ernesto-g/arduinosynth2/Hardware/PCB/Sketch_etch_silk_bottom.pdf

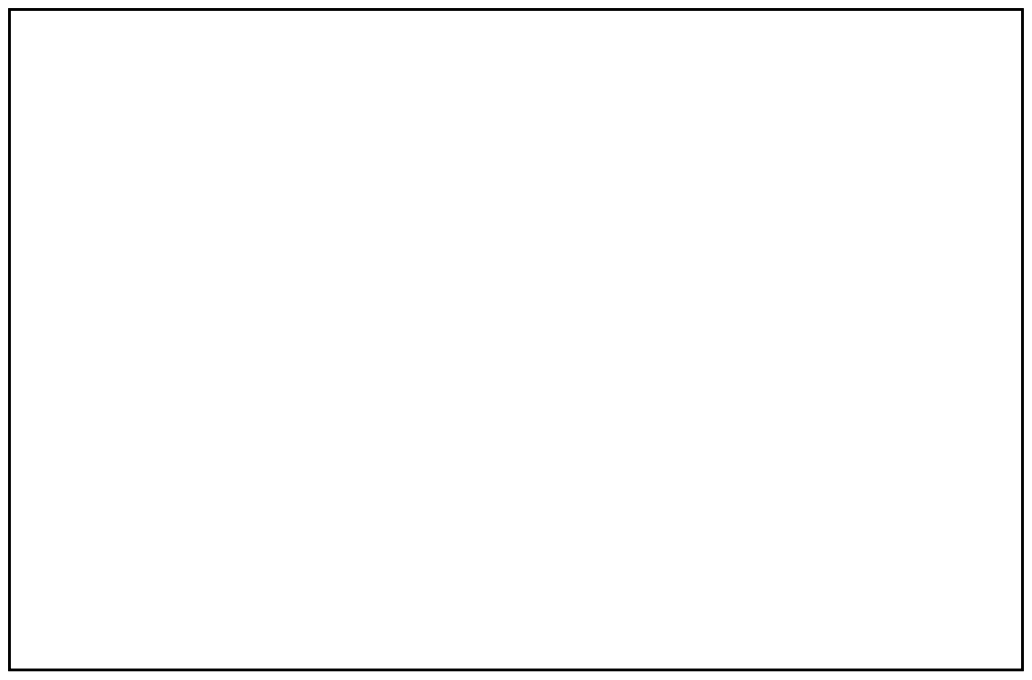
[picture p11: page 1]
