ernesto-g/arduinosynth2/Hardware/PCB/Sketch_etch_silk_top.pdf

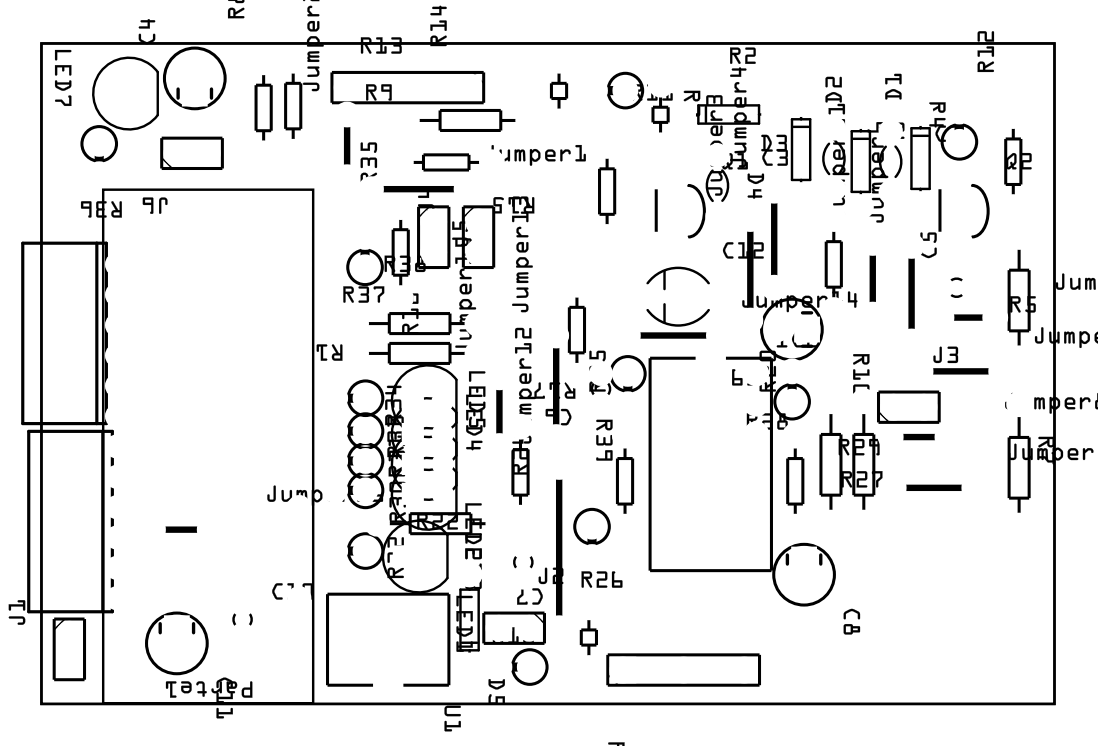
[picture p12: page 1]
