ernesto-g/arduinosynth2/Hardware/PCB/Sketch_etch_silk_top_mirror.pdf

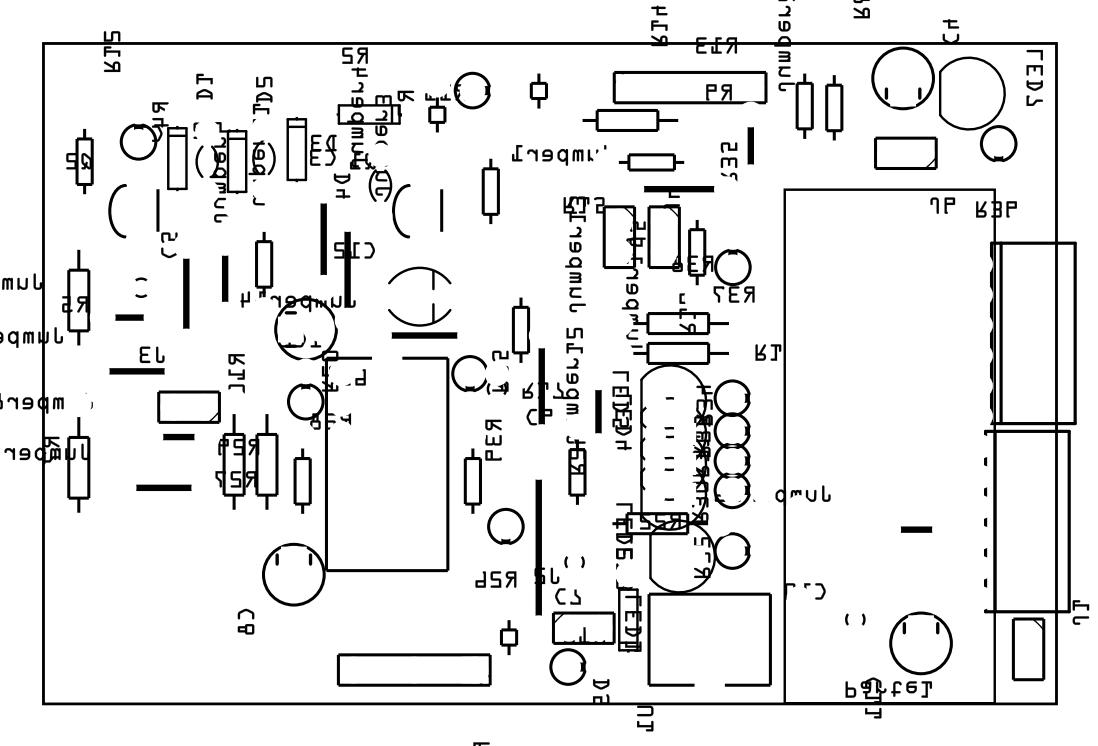
[picture p13: page 1]
