ernesto-g/arduinosynth2/Firmware/Main/Lfo.cpp

/**
 *  Arduino Digital Synth with analog filter
    Copyright (C) <2017>  Ernesto Gigliotti <ernestogigliotti@gmail.com>

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
    You should have received a copy of the GNU General Public License
    along with this program.  If not, see <http://www.gnu.org/licenses/>.
 */
//#include <HardwareSerial.h>
#include <Arduino.h>
#include <avr/pgmspace.h>
#include "Config.h"
#include "Lfo.h"
#include "VCOs.h"


#define TABLE_SIZE  3072
const unsigned char SINETABLE[TABLE_SIZE] PROGMEM = {0x80,0x80,0x80,0x80,0x81,0x81,0x81,0x81,0x82,0x82,0x82,0x82,0x83,0x83,0x83,0x83,0x84,0x84,0x84,0x84,0x85,0x85,0x85,0x85,0x86,0x86,0x86,0x87,0x87,0x87,0x87,0x88,
0x88,0x88,0x88,0x89,0x89,0x89,0x89,0x8a,0x8a,0x8a,0x8a,0x8b,0x8b,0x8b,0x8b,0x8c,0x8c,0x8c,0x8d,0x8d,0x8d,0x8d,0x8e,0x8e,0x8e,0x8e,0x8f,0x8f,0x8f,0x8f,0x90,0x90,
0x90,0x90,0x91,0x91,0x91,0x91,0x92,0x92,0x92,0x92,0x93,0x93,0x93,0x93,0x94,0x94,0x94,0x95,0x95,0x95,0x95,0x96,0x96,0x96,0x96,0x97,0x97,0x97,0x97,0x98,0x98,0x98,
0x98,0x99,0x99,0x99,0x99,0x9a,0x9a,0x9a,0x9a,0x9b,0x9b,0x9b,0x9b,0x9c,0x9c,0x9c,0x9c,0x9d,0x9d,0x9d,0x9d,0x9e,0x9e,0x9e,0x9e,0x9f,0x9f,0x9f,0x9f,0xa0,0xa0,0xa0,
0xa0,0xa1,0xa1,0xa1,0xa2,0xa2,0xa2,0xa2,0xa3,0xa3,0xa3,0xa3,0xa4,0xa4,0xa4,0xa4,0xa5,0xa5,0xa5,0xa5,0xa6,0xa6,0xa6,0xa6,0xa7,0xa7,0xa7,0xa7,0xa7,0xa8,0xa8,0xa8,
0xa8,0xa9,0xa9,0xa9,0xa9,0xaa,0xaa,0xaa,0xaa,0xab,0xab,0xab,0xab,0xac,0xac,0xac,0xac,0xad,0xad,0xad,0xad,0xae,0xae,0xae,0xae,0xaf,0xaf,0xaf,0xaf,0xb0,0xb0,0xb0,
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
0xcf,0xcf,0xcf,0xcf,0xcf,0xcf,0xcf,0xcf,0xcf,0xcf,0xcf,0xd0,0xd0,0xd0,0xd0,0xd0,0xd0,0xd0,0xd0,0xd0,0xd0,0xd0,0xd0,0xd0,0xd0,0xd0,0xd0,0xd1,0xd1,0xd1,0xd1,0xd1,
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
  };

const unsigned char FMULTI_POT_TABLE[256] PROGMEM = {1,1,1,1,1,1,1,1,1,1,2,2,2,2,2,2,2,2,2,2,3,3,3,3,3,3,3,3
,3,3,4,4,4,4,4,4,4,4,4,4,5,5,5,5,5,5,5,5,5,5,6,6,6,6,6,6,6,6,6,7,7,7,7
,7,7,7,7,7,7,7,8,8,8,8,8,8,8,8,8,8,9,9,9,9,9,9,9,9,9,9,10,10,10,10,10
,10,10,10,10,10,11,11,11,11,11,11,11,12,12,12,12,12,12,13,13,13,13,13
,13,14,14,14,14,14,14,15,15,15,15,15,15,16,16,16,16,17,17,17,17,18,18
,18,18,19,19,19,19,20,20,20,21,21,21,22,22,22,23,23,23,24,24,24,25,25
,25,26,26,26,27,27,27,28,28,28,29,29,29,30,30,30,31,31,31,32,32,32,33
,33,33,34,34,34,35,35,35,36,36,36,37,37,38,38,39,39,40,40,40,41,41,41
,42,42,42,43,43,43,44,44,44,45,45,45,46,46,46,47,47,47,48,48,48,49,49
,49,50,50,51,51,52,52,53,53,54,54,55,55,56,56,57,57,58,58,59,59,60,60};


static volatile unsigned char waveType=LFO_WAVE_TYPE_SINE;
static volatile unsigned int lfoCounter=0;
static volatile unsigned int freqMultiplier;

extern volatile unsigned int repeatCounter;
extern volatile unsigned int btnPressedCounter;
extern volatile unsigned int sequenceNoteDurationCounter;
static volatile unsigned int repeatCounterMultiplier;

static volatile unsigned char lfoIntDivider=0;
static volatile unsigned char lfoOn=0;
static volatile unsigned char lfoWaitZero=1;

// VCA modulation
extern volatile unsigned char lfoValueForVCAInPanel; // 127 max
extern volatile unsigned char lfoValueForVCA; // 128 max
//_____
// VCF modulation
extern volatile unsigned short lfoEg2BalanceValueForVCFInPanel; // 127 max
extern volatile unsigned short eg[EGS_LEN];
//________________


ISR(TIMER0_COMPA_vect) // 52uS
{
  digitalWrite(13,HIGH);  
  vcos_calculateOuts();
  lfoIntDivider++; 
  digitalWrite(13,LOW);  

}

void lfo_cooperativeTimer0Interrupt(void)
{
  unsigned short PWMValue;
  if(lfoIntDivider>=12)
  {
    lfoIntDivider=0;
     
      lfoCounter+=freqMultiplier;
      if(lfoCounter>=TABLE_SIZE){
        lfoCounter=lfoCounter - TABLE_SIZE;
      }
    
      switch(waveType)
      {
        case LFO_WAVE_TYPE_SINE:
          PWMValue = pgm_read_byte_near(SINETABLE + lfoCounter );
          break;
        case LFO_WAVE_TYPE_TRIANGLE:
          PWMValue = pgm_read_byte_near(TRIANGLETABLE + lfoCounter );
          break;
        case LFO_WAVE_TYPE_EXP:
          PWMValue = pgm_read_byte_near(EXPTABLE + lfoCounter );
          break;
        case LFO_WAVE_TYPE_SQUARE:
          if(lfoCounter<(TABLE_SIZE/2))
            PWMValue = 255;
          else
            PWMValue = 0;
          break;
      }  

      // VCA modulation
      lfoValueForVCA = PWMValue/2;
      //________________

      // VCF modulation (analog)
      if(lfoOn)
      {
        //OCR2B = PWMValue;
        PWMValue = ((PWMValue)*lfoEg2BalanceValueForVCFInPanel)/128;
      }
      else
      {
          if(lfoWaitZero)
          {
              PWMValue = ((PWMValue)*lfoEg2BalanceValueForVCFInPanel)/128;
              //OCR2B = PWMValue;
              if(PWMValue==0)
                lfoWaitZero=0;
          }
          else 
            PWMValue = 0;
      }
      OCR2B = PWMValue + (((eg[EG2_INDEX]))*((128-lfoEg2BalanceValueForVCFInPanel)))/128;
      //_________________

      repeatCounterMultiplier++;
      if(repeatCounterMultiplier>=40) // 25ms
      {
        repeatCounterMultiplier=0;
        repeatCounter++;
        btnPressedCounter++;
        sequenceNoteDurationCounter++;
      }
  }

}

void lfo_init(void)
{
    waveType=LFO_WAVE_TYPE_SINE;
    lfoCounter=0;
    freqMultiplier=30;  // from 1 to 60 for 0.5Hz to 30Hz
    repeatCounterMultiplier=0;
    repeatCounter=0;
}

void lfo_setWaveType(unsigned char type)
{
    waveType = type;
}

/**
 * fm: 0 to 255
 */
void lfo_setFrequencyMultiplier(unsigned int fm)
{   
    freqMultiplier = pgm_read_byte_near(FMULTI_POT_TABLE + fm);    
}

void lfo_reset(void)
{
    if(lfoOn==0)
      lfoCounter=0;
}

void lfo_outOn(void)
{
  lfoOn=1;
  lfoWaitZero=0;
}
void lfo_outOff(void)
{
  if(lfoOn)
  {
    lfoWaitZero=1;  
    lfoOn=0;
  }
}
